mcleod-ideafix/divtiesus/cpld/zxunoregs.v

`timescale 1ns / 1ns
`default_nettype none

//    This file is part of the ZXUNO Spectrum core. 
//    Creation date is 23:37:21 2014-03-01 by Miguel Angel Rodriguez Jodar
//    (c)2014-2020 ZXUNO association.
//    ZXUNO official repository: http://svn.zxuno.com/svn/zxuno
//    Username: guest   Password: zxuno
//    Github repository for this core: https://github.com/mcleod-ideafix/zxuno_spectrum_core
//
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
//    Any distributed copy of this file must keep this notice intact.

module zxunoregs (
   input wire clk,
   input wire rst_n,
   input wire [15:0] a,
   input wire iorq_n,
   input wire rd_n,
   input wire wr_n,
   //input wire m1_n,
   inout wire [7:0] d,
   output reg [7:0] addr,
   output wire read_from_reg,
   output wire write_to_reg
   );
   
`include "config.vh"

// Manages register addr ($00 - $FF) 
  wire iorq_wr = iorq_n | wr_n;  
  always @(posedge iorq_wr or negedge rst_n) begin
    if (rst_n == 1'b0)
      addr <= 8'h00;
   else if (a == IOADDR)
      addr <= d;
  end
  
  //assign d = (iorq_n == 1'b0 && a==IOADDR && rd_n == 1'b0 && wr_n == 1'b1 && m1_n == 1'b1)? addr : 8'hZZ;

  assign read_from_reg = (a==IODATA && iorq_n == 1'b0 && rd_n == 1'b0);
  assign write_to_reg = (a==IODATA && iorq_n == 1'b0 && wr_n == 1'b0);
endmodule
